edabngl/UC2_OCT/1.Experimental_Process/Modules/10.XY Linear Stage with Motors/00_micrometer_moun_xystage_china_new.stl

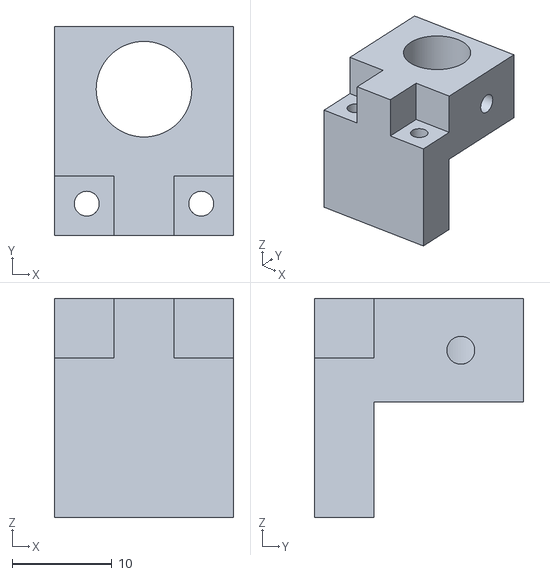
[picture p20: CAD file, 2023-02-13]
1.Experimental_Process/Modules/10.XY Linear Stage with Motors/00_micrometer_moun_xystage_china_new.stl
18.0 x 21.0 x 22.0
