edabngl/UC2_OCT/1.Experimental_Process/Modules/11.Base Cube and Others/10_Lid_2x1_v3.stl

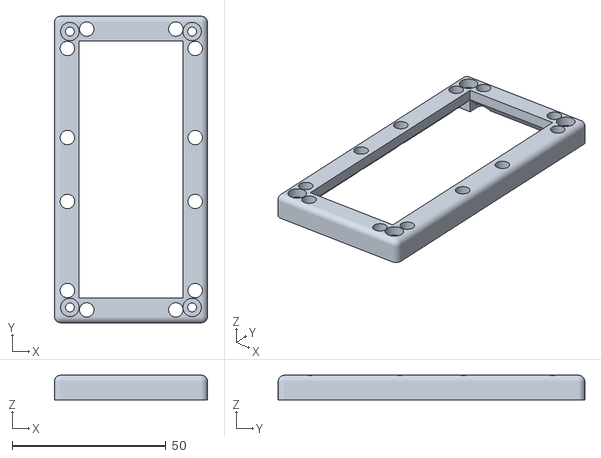
[picture p21: CAD file, 2023-02-13]
1.Experimental_Process/Modules/11.Base Cube and Others/10_Lid_2x1_v3.stl
49.8 x 99.8 x 8.00
