edabngl/UC2_OCT/1.Experimental_Process/Modules/4.Adjustable Z Stage Modules/X direction/30_Cube_Z_Focus_NEMA8_captive_base_v0.stl

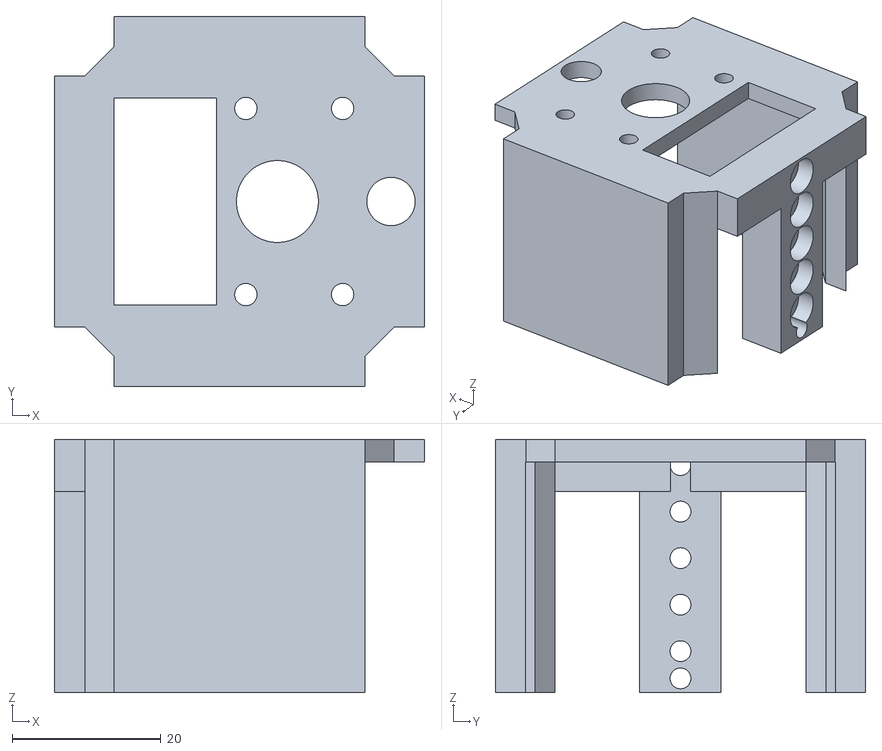
[picture p22: CAD file, 2023-02-13]
1.Experimental_Process/Modules/4.Adjustable Z Stage Modules/X direction/30_Cube_Z_Focus_NEMA8_captive_base_v0.stl
49.7 x 49.7 x 34.0
