edabngl/UC2_OCT/1.Experimental_Process/Modules/4.Adjustable Z Stage Modules/XZ directions/20_Cube_Insert_Z_Stage_XY_Stage_springblock.stl

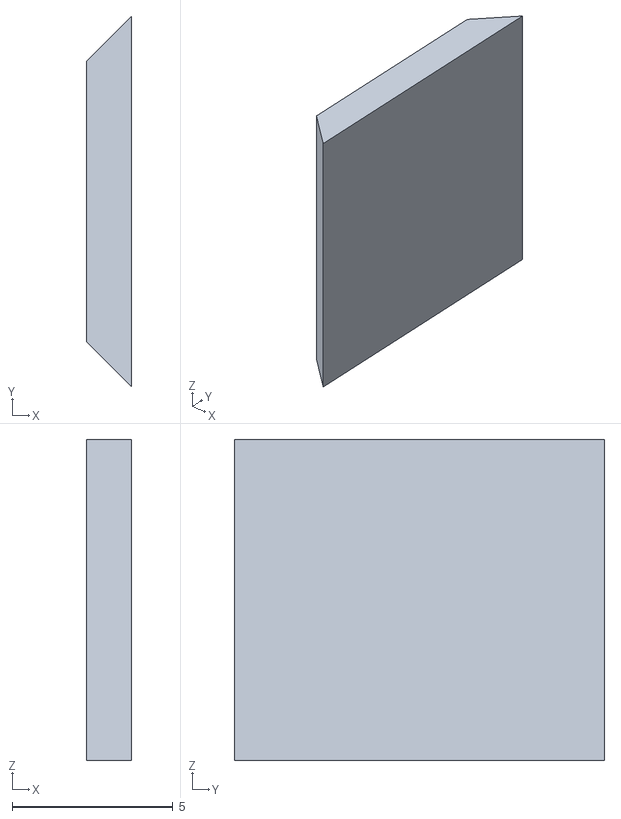
[picture p23: CAD file, 2023-02-13]
1.Experimental_Process/Modules/4.Adjustable Z Stage Modules/XZ directions/20_Cube_Insert_Z_Stage_XY_Stage_springblock.stl
1.40 x 11.5 x 10.00
