edabngl/UC2_OCT/1.Experimental_Process/Modules/5.Sample Mirror Holder Module/20_Cube_Insert_Kinematic_Mirror_90_pro_magnetic.stl

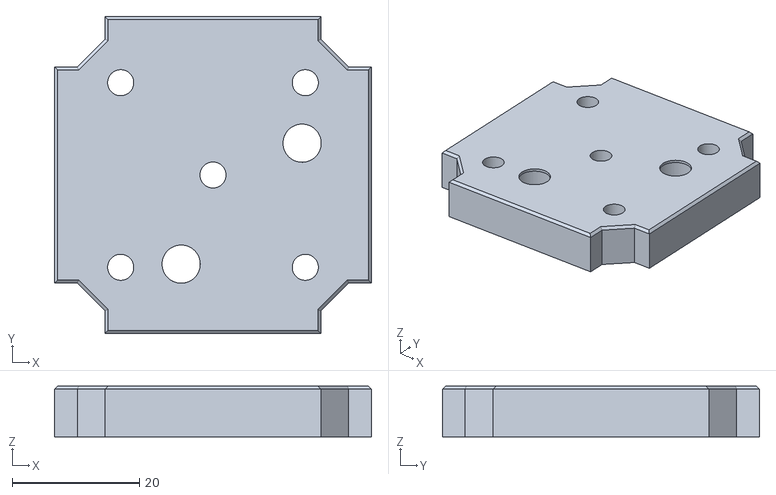
[picture p24: CAD file, 2023-02-13]
1.Experimental_Process/Modules/5.Sample Mirror Holder Module/20_Cube_Insert_Kinematic_Mirror_90_pro_magnetic.stl
49.8 x 49.8 x 8.00
