edabngl/UC2_OCT/1.Experimental_Process/Modules/6.Reference Mirror Module/M12 VCA/M12 lens holder.STEP

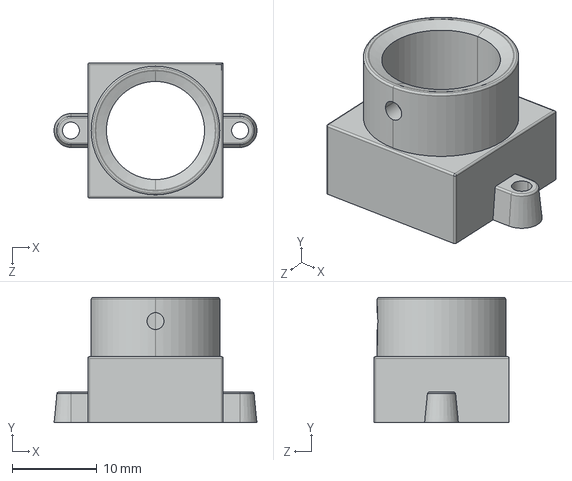
[picture p25: CAD file, 2023-02-13]
1.Experimental_Process/Modules/6.Reference Mirror Module/M12 VCA/M12 lens holder.STEP
24.0 x 14.8 x 16.0 mm
