edabngl/UC2_OCT/1.Experimental_Process/Modules/6.Reference Mirror Module/UC2 VCA/20_Cube_Insert_VCA_base_lower_v0.stl

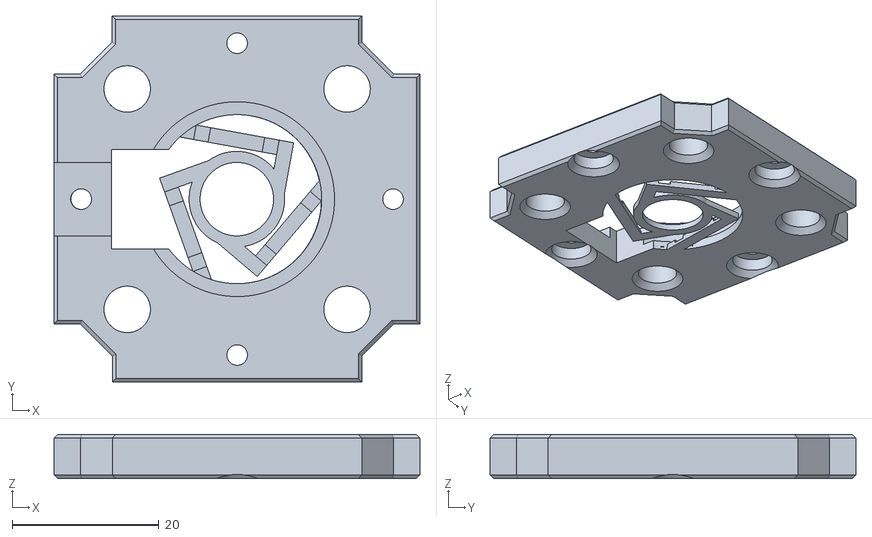
[picture p26: CAD file, 2023-02-13]
1.Experimental_Process/Modules/6.Reference Mirror Module/UC2 VCA/20_Cube_Insert_VCA_base_lower_v0.stl
49.8 x 49.8 x 6.00
