edabngl/UC2_OCT/1.Experimental_Process/Modules/8.Kinematic Mirror Holder Module/20_Cube_Insert_Kinematic_KES400AMount_45_small_v3.stl

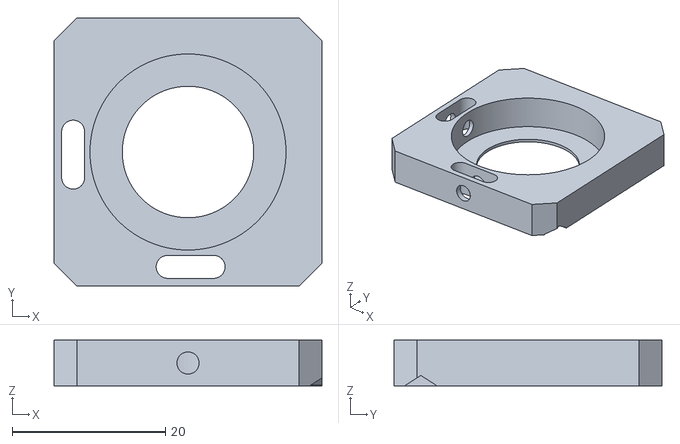
[picture p27: CAD file, 2023-02-13]
1.Experimental_Process/Modules/8.Kinematic Mirror Holder Module/20_Cube_Insert_Kinematic_KES400AMount_45_small_v3.stl
35.0 x 35.0 x 6.00
