edabngl/UC2_OCT/1.Experimental_Process/Modules/10.XY Linear Stage with Motors/00_XY_stage-CHUO_SEIKI_LD-647-R1-Bottom.stl

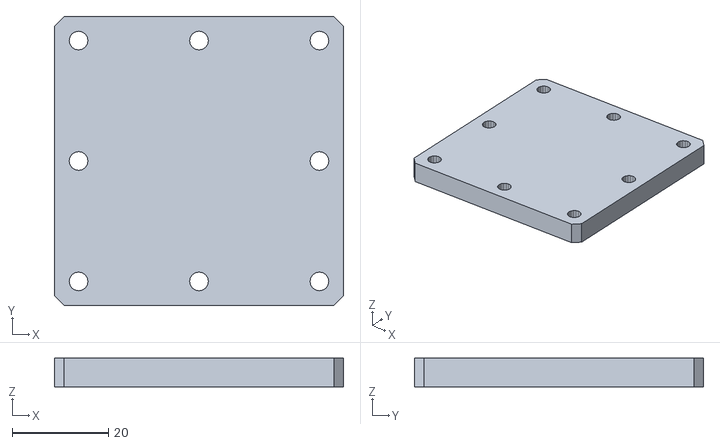
[picture p28: CAD file, 2023-02-13]
1.Experimental_Process/Modules/10.XY Linear Stage with Motors/00_XY_stage-CHUO_SEIKI_LD-647-R1-Bottom.stl
60.0 x 60.0 x 6.00
