edabngl/UC2_OCT/1.Experimental_Process/Modules/11.Base Cube and Others/10_Cube_2x1_v3.stl

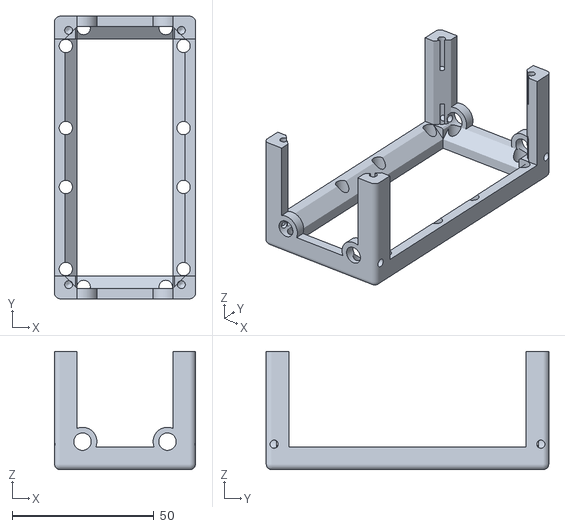
[picture p29: CAD file, 2023-02-13]
1.Experimental_Process/Modules/11.Base Cube and Others/10_Cube_2x1_v3.stl
49.8 x 99.8 x 41.8
