edabngl/UC2_OCT/1.Experimental_Process/Modules/4.Adjustable Z Stage Modules/X direction/30_Cube_Cube_Z_Focus_MGN_NEMA_belt_pushing_slide_LONGER_up_UPDipt.stl

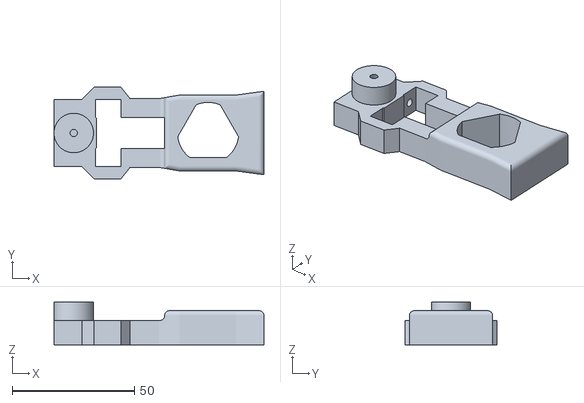
[picture p30: CAD file, 2023-02-13]
1.Experimental_Process/Modules/4.Adjustable Z Stage Modules/X direction/30_Cube_Cube_Z_Focus_MGN_NEMA_belt_pushing_slide_LONGER_up_UPDipt.stl
85.8 x 37.4 x 17.5
