edabngl/UC2_OCT/1.Experimental_Process/Modules/6.Reference Mirror Module/M12 VCA/20_Cube_Insert_M12_VCAmount_inside.stl

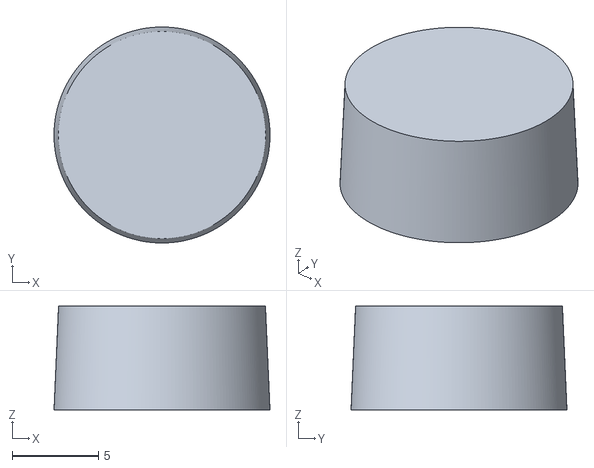
[picture p31: CAD file, 2023-02-13]
1.Experimental_Process/Modules/6.Reference Mirror Module/M12 VCA/20_Cube_Insert_M12_VCAmount_inside.stl
12.5 x 12.5 x 6.00
