edabngl/UC2_OCT/1.Experimental_Process/Modules/10.XY Linear Stage with Motors/30_XY_Sample_arm_UC2_Adapter_Lighter_v3.stl

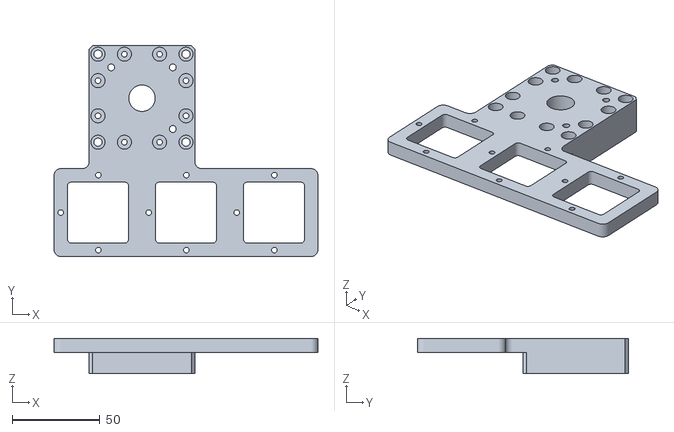
[picture p32: CAD file, 2023-02-13]
1.Experimental_Process/Modules/10.XY Linear Stage with Motors/30_XY_Sample_arm_UC2_Adapter_Lighter_v3.stl
150.0 x 120.0 x 20.0
