edabngl/UC2_OCT/1.Experimental_Process/Modules/11.Base Cube and Others/Cube_Insert_Alignment_Tool_centered_Pinhole.stl

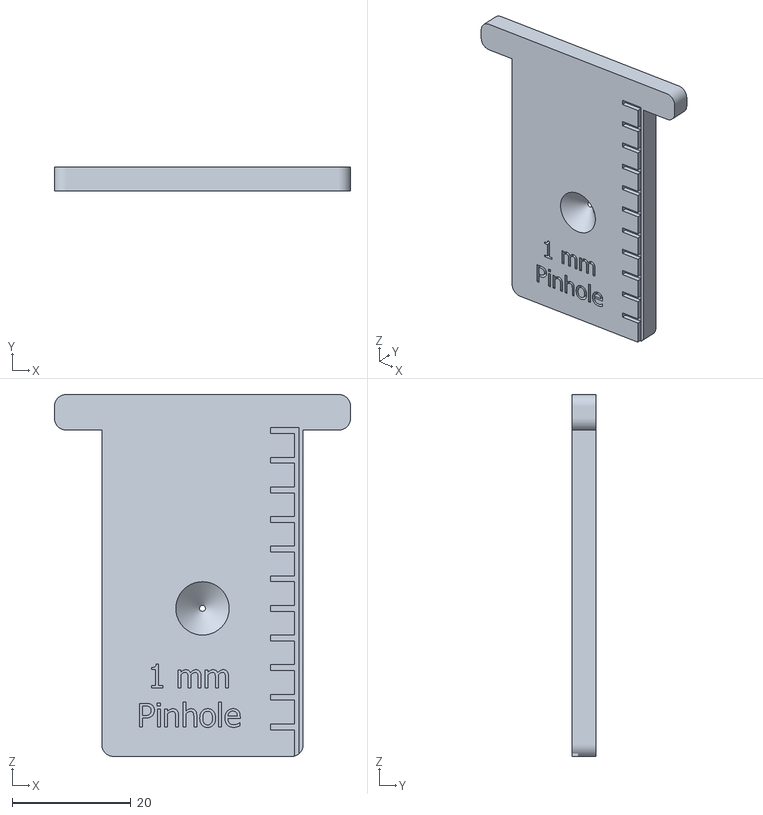
[picture p33: CAD file, 2023-02-13]
1.Experimental_Process/Modules/11.Base Cube and Others/Cube_Insert_Alignment_Tool_centered_Pinhole.stl
50.0 x 4.00 x 61.1
