edabngl/UC2_OCT/1.Experimental_Process/Modules/10.XY Linear Stage with Motors/30_cellSTORM_UC2_motorized_xystage_spacer_thicker.stl

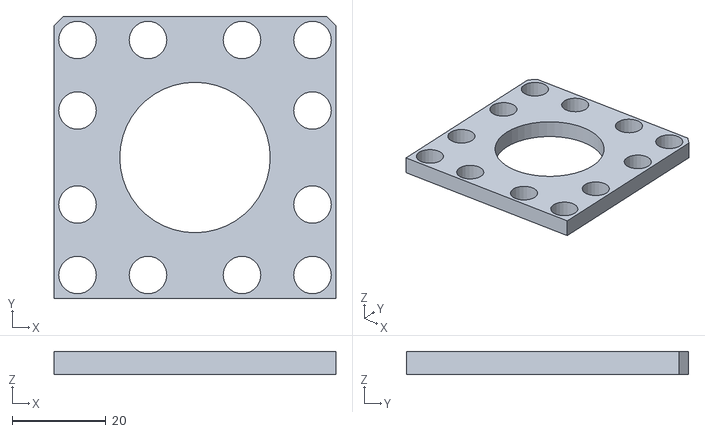
[picture p34: CAD file, 2023-02-13]
1.Experimental_Process/Modules/10.XY Linear Stage with Motors/30_cellSTORM_UC2_motorized_xystage_spacer_thicker.stl
60.0 x 60.0 x 5.00
