edabngl/UC2_OCT/1.Experimental_Process/Modules/10.XY Linear Stage with Motors/30_cellSTORM_UC2_motorized_micrometer_gear1.stl

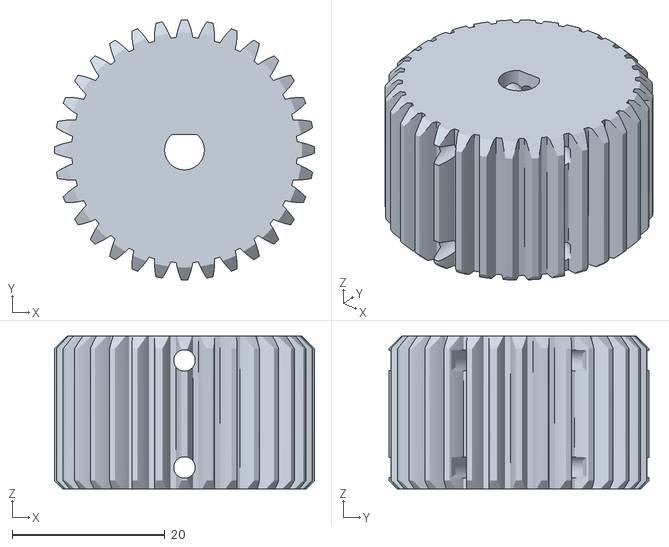
[picture p36: CAD file, 2023-02-13]
1.Experimental_Process/Modules/10.XY Linear Stage with Motors/30_cellSTORM_UC2_motorized_micrometer_gear1.stl
34.0 x 34.0 x 20.0
