edabngl/UC2_OCT/2.Results/IMAGES/Interferogram_4step_M12.png

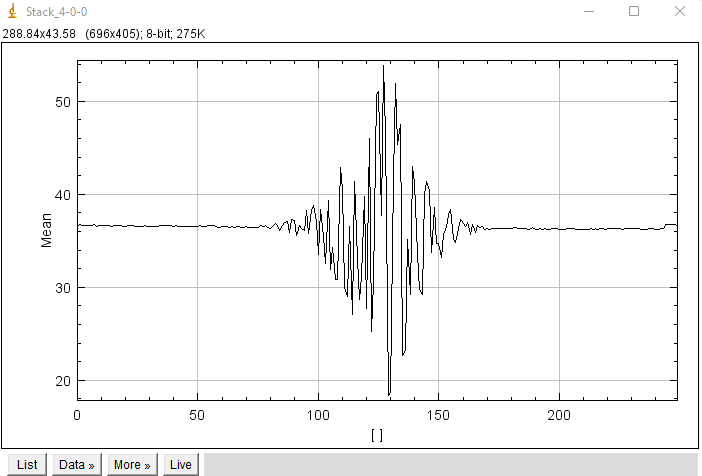
2.Results/IMAGES/Interferogram_4step_M12.png
