edabngl/UC2_OCT/2.Results/IMAGES/RES_alg_step5.jpg

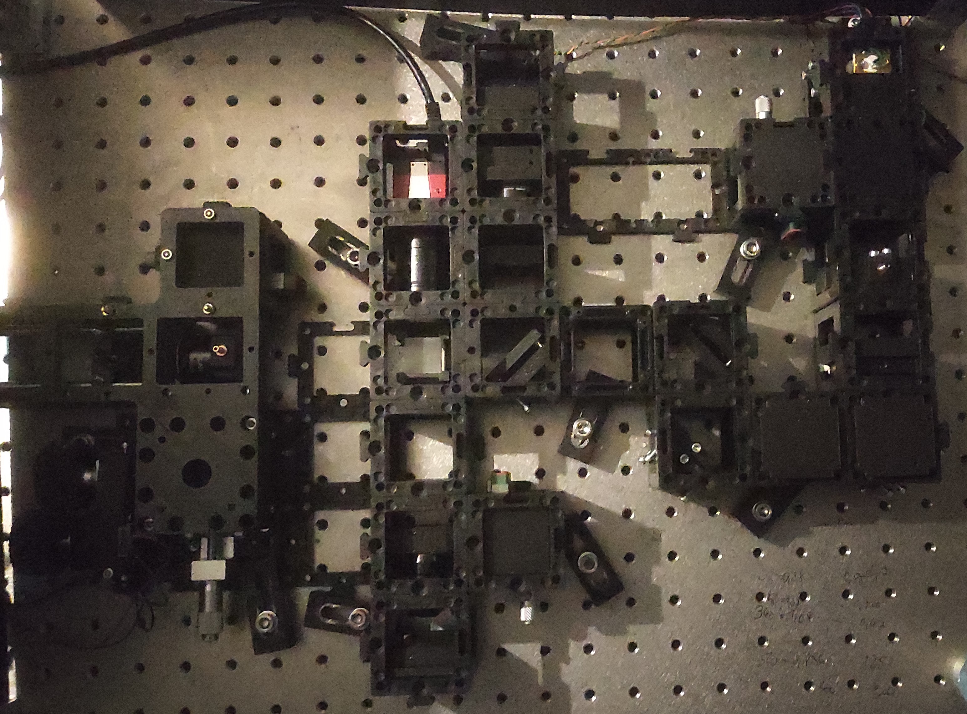
2.Results/IMAGES/RES_alg_step5.jpg
