edabngl/UC2_OCT/1.Experimental_Process/Modules/1.Light Source Modules/1.LASER/README.md

# LASER

Pen-lasers were used in the begging for the alignment , blue UV and green VIS lasers. Green laser was so powerful. I tried to reduce the power using ND filter but instead of that I changed the laser.

In the alignment part of the Thorlabs setup, [RGB Laser source]() was used with red paper filter.

*Properties of the RGB Laser*
  -
  -

Spectrum of the RGB Laser:

<p align="middle">
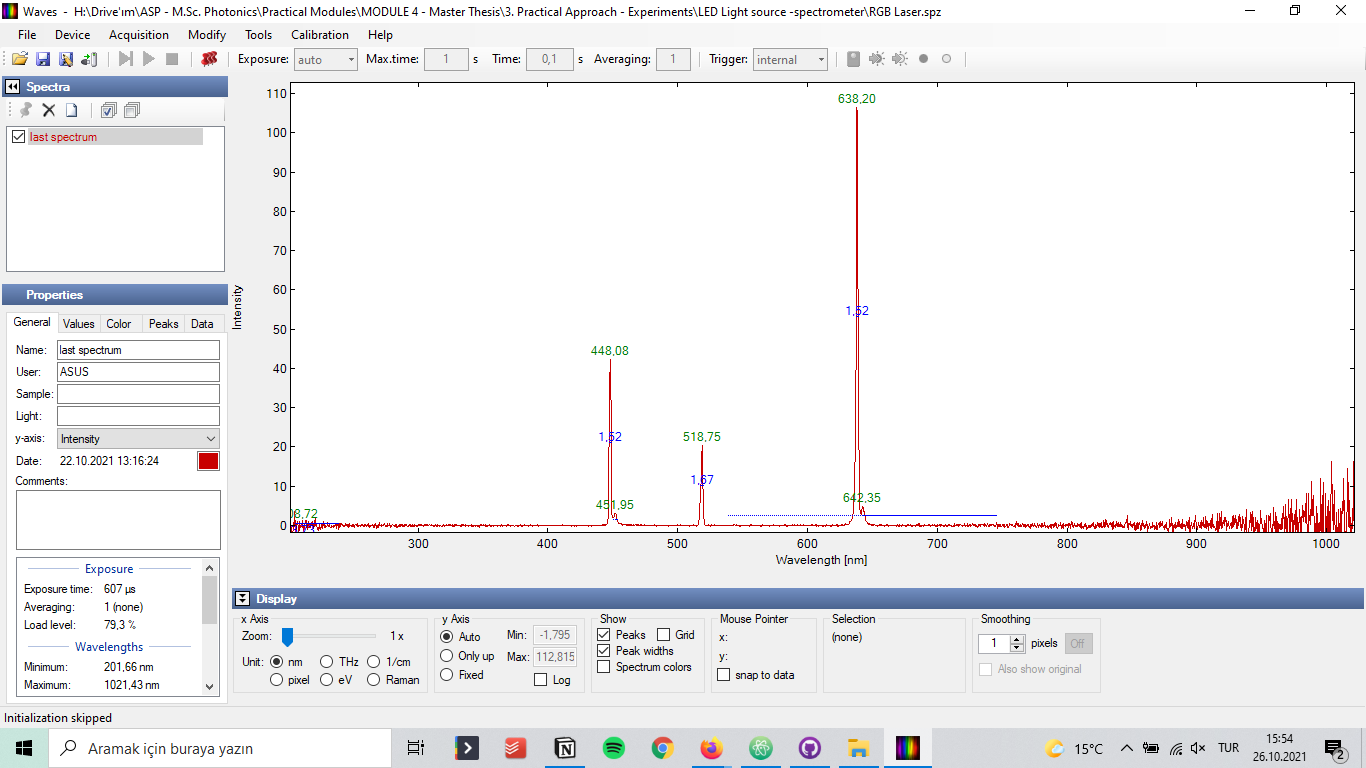
[picture p54: 1.Experimental_Process/Modules/1.Light Source Modules/1.LASER/IMAGES/RGB Laser spectrum.PNG]

</p>

Spectrum of the RGB Laser with red paper filter:

<p align="middle">
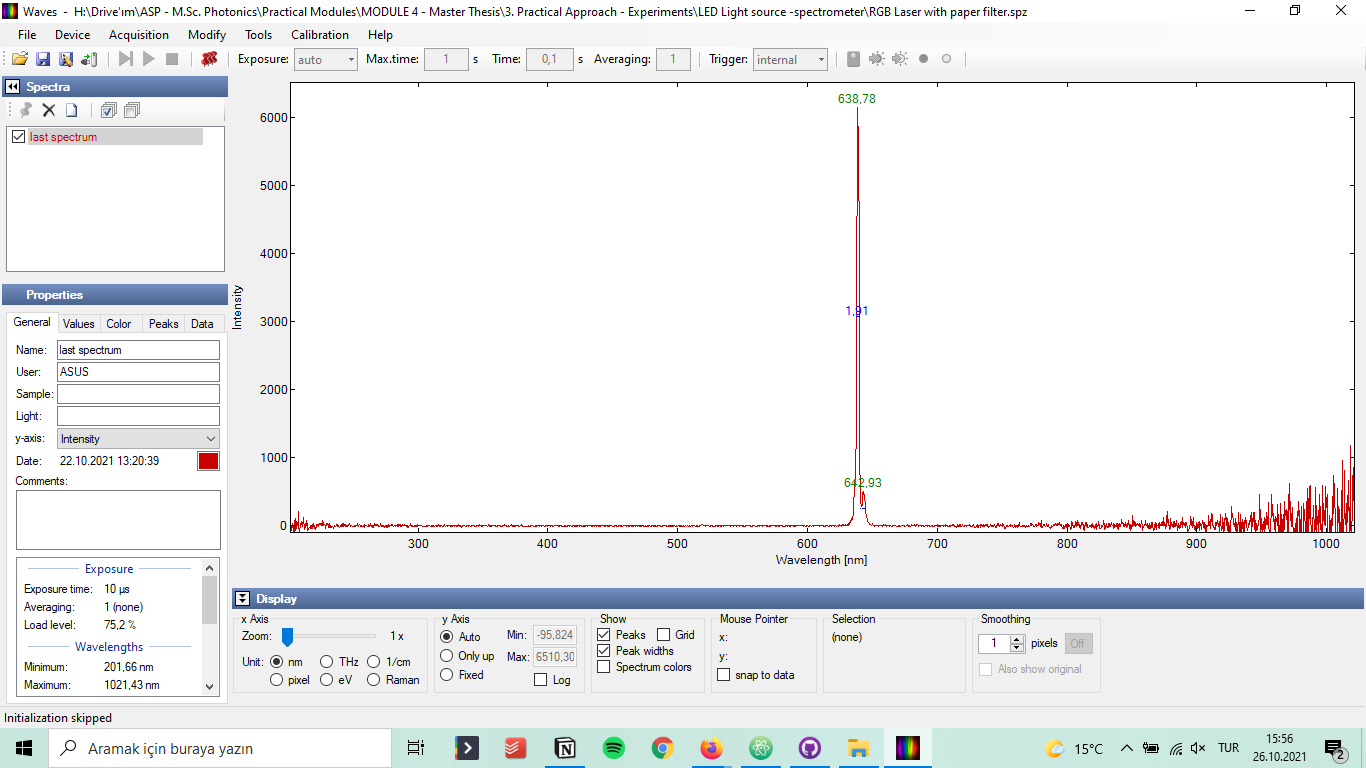
[picture p55: 1.Experimental_Process/Modules/1.Light Source Modules/1.LASER/IMAGES/RGB Laser with paper filter spectrum.PNG]

</p>

## Collaborating
If you find this project useful, please like this repository, follow us on Twitter and cite the webpage! :-)
