edabngl/UC2_OCT/1.Experimental_Process/Alignment_Procedure/IMAGES/algn_1.png

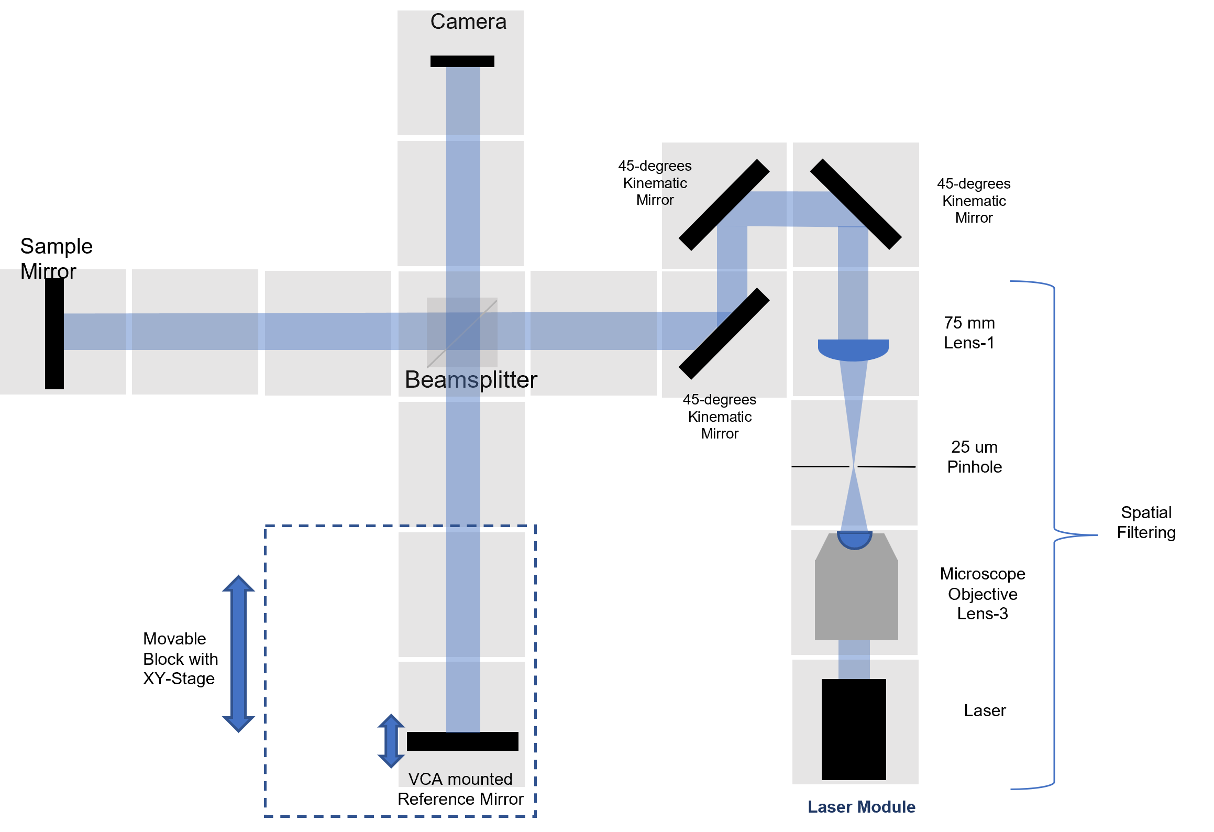
1.Experimental_Process/Alignment_Procedure/IMAGES/algn_1.png
