edabngl/UC2_OCT/1.Experimental_Process/IMAGES/Application_Full-Fiedld_Time_Domain_OCT_combined_UC2-VCA.png

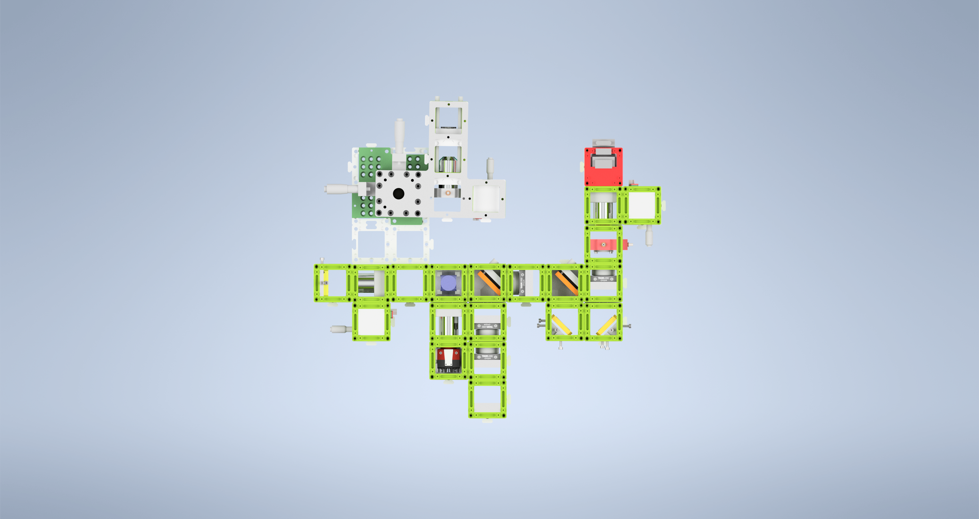
1.Experimental_Process/IMAGES/Application_Full-Fiedld_Time_Domain_OCT_combined_UC2-VCA.png
