edabngl/UC2_OCT/1.Experimental_Process/IMAGES/Application_Full-Field_Time_Domain_OCT_combined_Thorlabs_Motors.png

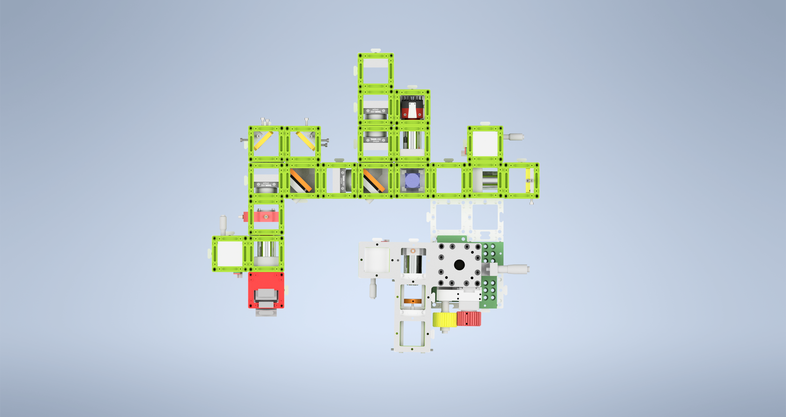
1.Experimental_Process/IMAGES/Application_Full-Field_Time_Domain_OCT_combined_Thorlabs_Motors.png
