edabngl/UC2_OCT/1.Experimental_Process/IMAGES/Laser_alignment_spatial_filtering.png

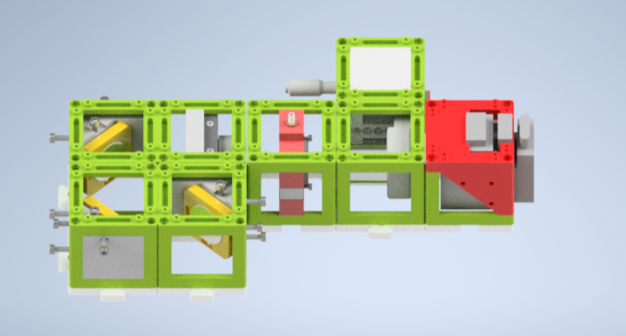
1.Experimental_Process/IMAGES/Laser_alignment_spatial_filtering.png
