edabngl/UC2_OCT/1.Experimental_Process/Modules/IMAGES/Reference_Modules.png

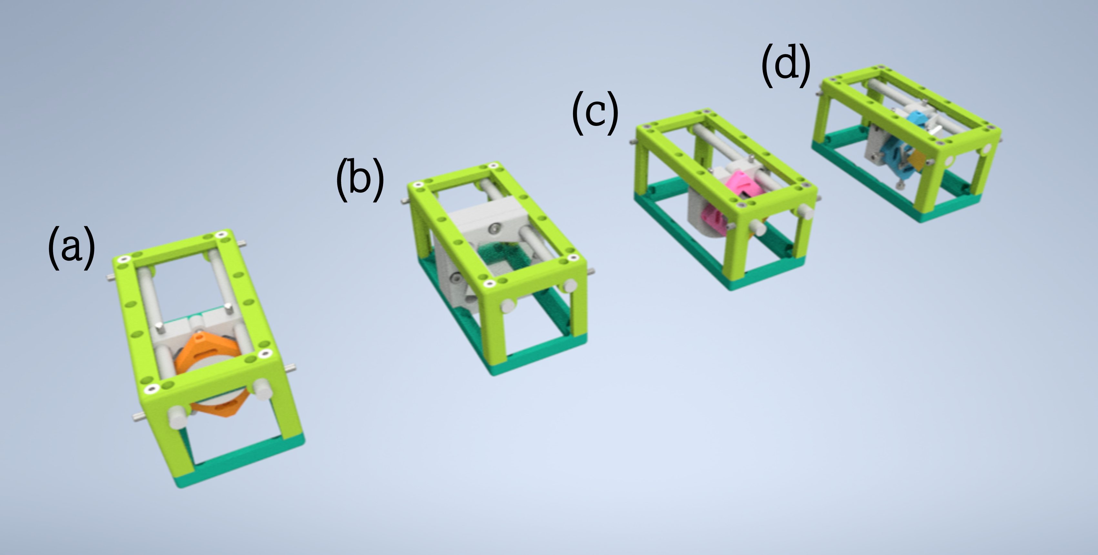
1.Experimental_Process/Modules/IMAGES/Reference_Modules.png
